emersonmello/doorlock_raspberrypi/extras/breadboard.jpg

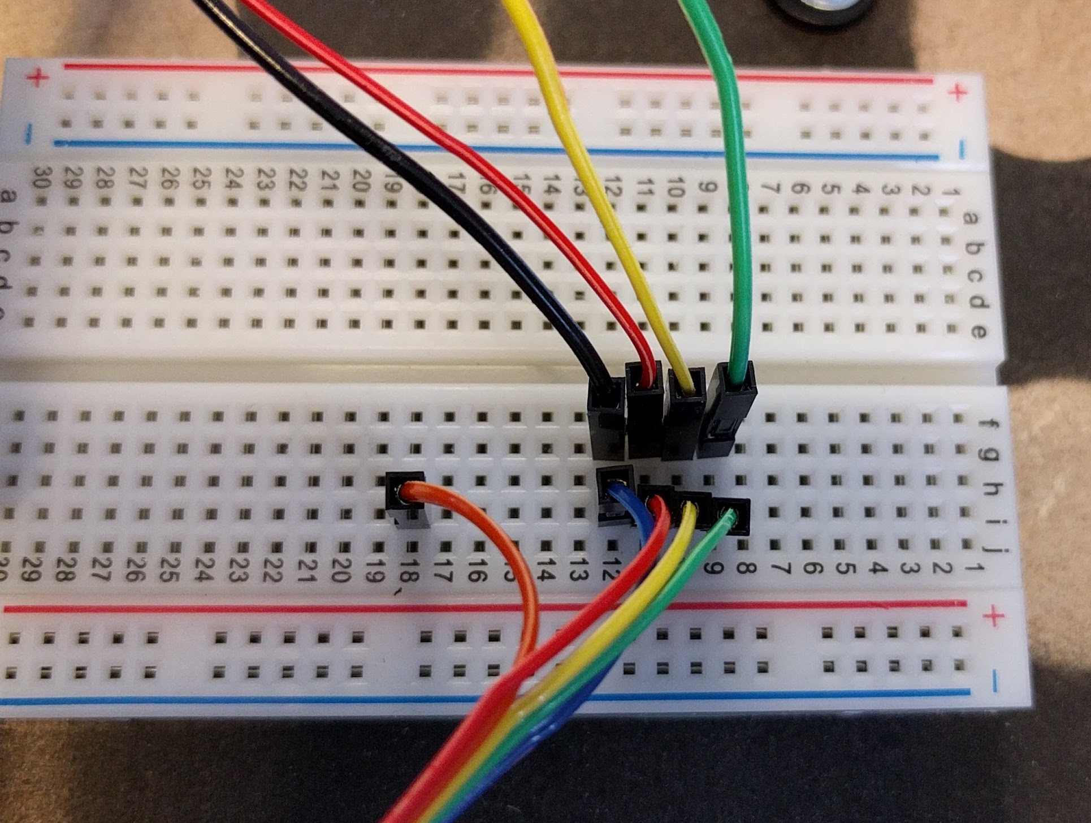
extras/breadboard.jpg
