emersonmello/doorlock_raspberrypi/extras/elechouse-pn532.png

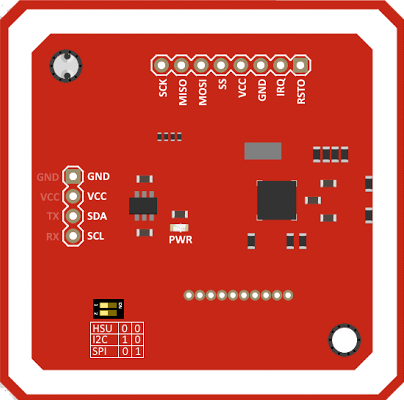
extras/elechouse-pn532.png
