emersonmello/doorlock_raspberrypi/extras/pn532.jpg

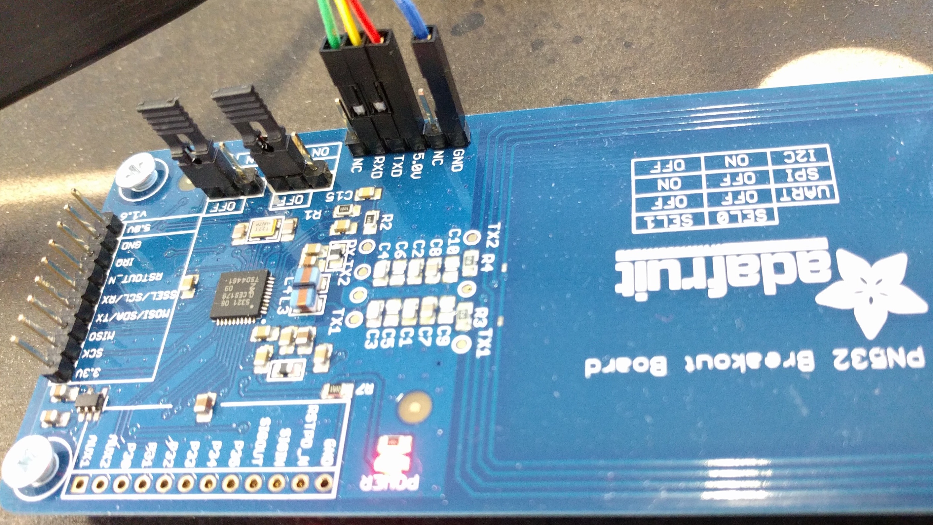
extras/pn532.jpg
